altJSV/CatFeeder/data/cat.png

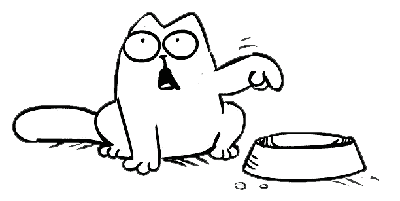
data/cat.png
